WiddleWabbit/MQTT-Module-PumpController/Outputs/Models/MQTT-Module-PumpController-Back.png

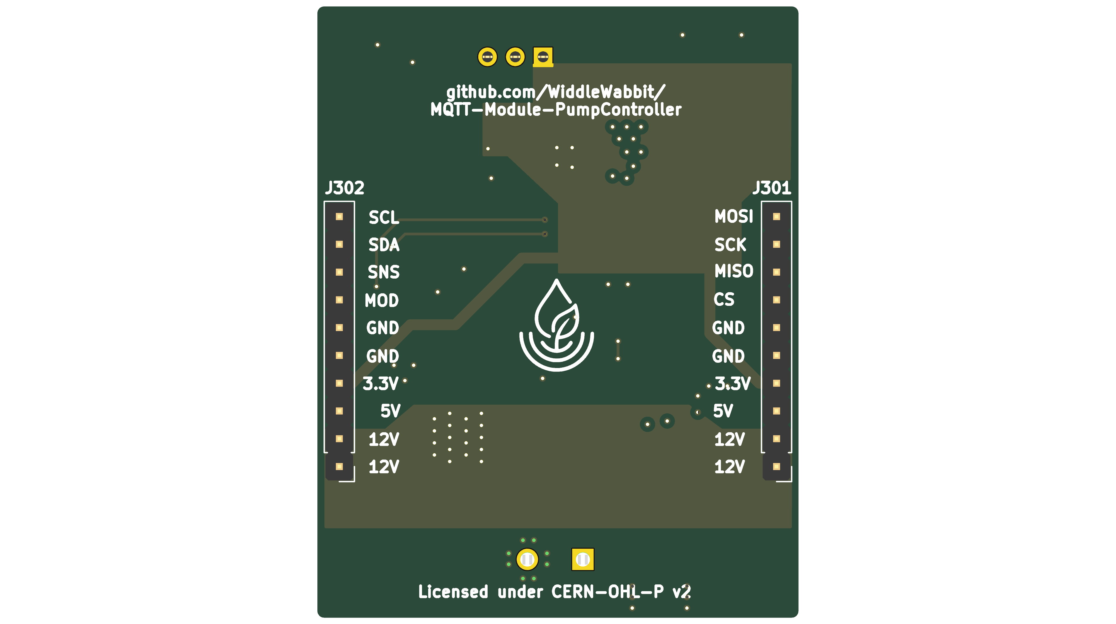
Outputs/Models/MQTT-Module-PumpController-Back.png
