WiddleWabbit/MQTT-Module-PumpController/Outputs/Models/MQTT-Module-PumpController-Front.png

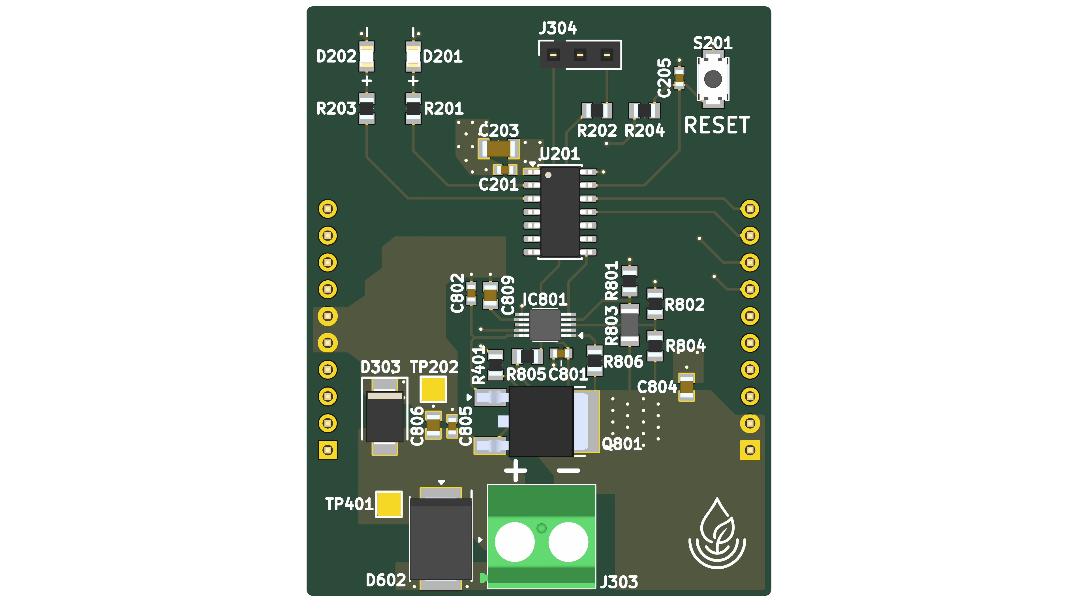
Outputs/Models/MQTT-Module-PumpController-Front.png
